SorinoSSK/Personal-Alarm-Device/Device Design/Schematic_1/Image/A9G_nobg.png

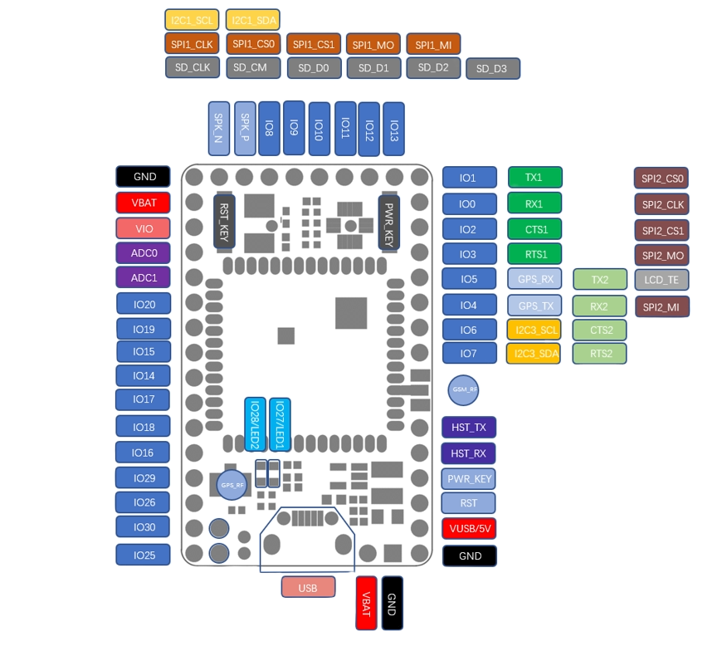
Device Design/Schematic_1/Image/A9G_nobg.png
