SorinoSSK/Personal-Alarm-Device/Arduino_Code/Main Code/GebirahHelpMainV2/SKRSSI.ino

static void getRSSIDistance(BLEDevice central)
{
    int rssiValue = RSSIMeanFilter(central.rssi());
    int reference = -63;
    float pathLoss = 3.0;
    float distance = pow(10, (reference - rssiValue)/(10*pathLoss));
    BleRSSIValu.setValue(String(distance) + ", " + String(rssiValue));
}
