SorinoSSK/Personal-Alarm-Device/Arduino_Code/Main Code/GebirahHelpMainV2/GebirahHelpMicrophone.ino

/**
 * Callback function to process the data from the PDM microphone.
 * NOTE: This callback is executed as part of an ISR.
 * Therefore using `Serial` to print messages inside this function isn't supported.
 * */
static void audio_rec_callback(uint16_t *buf, uint32_t buf_len) 
{    
    // Copy samples from DMA buffer to inference buffer

    static uint32_t idx = 0;

    if (recording) {
        for (uint32_t i = 0; i < buf_len; i++) 
        {
        
        #if defined(WIO_TERMINAL)
            // Convert 12-bit unsigned ADC value to 16-bit PCM (signed) audio value
            recording_buf[idx++] = filter.step((int16_t)(buf[i] - 1024) * 16);    //with Filter
            //recording_buf[idx++] = (int16_t)(buf[i] - 1024) * 16;               // without filter
        #elif defined(ARDUINO_ARCH_NRF52840)
            recording_buf[idx++] = buf[i];
        #endif
                
            if (idx >= SAMPLES)
            { 
                idx = 0;
                recording = 0;
                record_ready = true;
                break;
            } 
        }
    }
}

static void MICInit1()
{
    #if defined(WIO_TERMINAL)
        pinMode(WIO_KEY_A, INPUT_PULLUP);
    #endif
    Mic.set_callback(audio_rec_callback);
}

static void MICInit2()
{
    if (!Mic.begin()) 
    {
        if (Debug_Status != 0)
        {
            Serial.println("Starting PDM MIC failed!");
        }
        while (1);
    }
    if (Debug_Status != 0)
    {
        Serial.println("Started PDM MIC!");
    }
}

// void microphoneFunction()
// {
//     if (samplesRead) 
//     {
//         // Use memcpy for bulk copy
//         memcpy(sampleBuffer1 + sample_cnt, sampleBuffer, samplesRead * sizeof(short));

//         sample_cnt += samplesRead;

//         if (sample_cnt >= SAMPLES) 
//         {
//             // Consider renaming MicRecordRdy for clarity
//             MicRecordRdy = true;
//             sample_cnt = 0;
//         }
//         samplesRead = 0;
//     }
// }
