SorinoSSK/Personal-Alarm-Device/Arduino_Code/IMU_Test/IMU_Test.ino

/*****************************************************************************/
//  HighLevelExample.ino
//  Hardware:      Grove - 6-Axis Accelerometer&Gyroscope
//	Arduino IDE:   Arduino-1.65
//	Author:	       Lambor
//	Date: 	       Oct,2015
//	Version:       v1.0
//
//  Modified by:
//  Data:
//  Description:
//
//	by www.seeedstudio.com
//
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
/*******************************************************************************/

#include "LSM6DS3.h"
#include "Wire.h"

//Create a instance of class LSM6DS3
LSM6DS3 myIMU(I2C_MODE, 0x6A);    //I2C device address 0x6A

void setup() {
    // put your setup code here, to run once:
    Serial.begin(9600);
    while (!Serial);
    //Call .begin() to configure the IMUs
    if (myIMU.begin() != 0) {
        Serial.println("Device error");
    } else {
        Serial.println("Device OK!");
    }
}

void loop() {
    //Accelerometer
    // Serial.print("\nAccelerometer:\n");
    // Serial.print(" X1 = ");
    // Serial.println(myIMU.readFloatAccelX(), 4);
    // Serial.print(" Y1 = ");
    // Serial.println(myIMU.readFloatAccelY(), 4);
    // Serial.print(" Z1 = ");
    // Serial.println(myIMU.readFloatAccelZ(), 4);
    float AccelX = myIMU.readFloatAccelX();
    float AccelY = myIMU.readFloatAccelY();
    float AccelZ = myIMU.readFloatAccelZ();
    Serial.print(AccelX);
    Serial.print(",");
    Serial.print(AccelY);
    Serial.print(",");
    Serial.print(AccelZ);
    Serial.print(",");
    Serial.println(sqrt(pow(AccelX, 2) + pow(AccelY, 2) + pow(AccelZ, 2)));
    // //Gyroscope
    // Serial.print("\nGyroscope:\n");
    // Serial.print(" X1 = ");
    // Serial.println(myIMU.readFloatGyroX(), 4);
    // Serial.print(" Y1 = ");
    // Serial.println(myIMU.readFloatGyroY(), 4);
    // Serial.print(" Z1 = ");
    // Serial.println(myIMU.readFloatGyroZ(), 4);

    // //Thermometer
    // Serial.print("\nThermometer:\n");
    // Serial.print(" Degrees C1 = ");
    // Serial.println(myIMU.readTempC(), 4);
    // Serial.print(" Degrees F1 = ");
    // Serial.println(myIMU.readTempF(), 4);

    // delay(1000);
}
